kmzbrnoI/mtb-rc/fw/src/railcom/railcom_ll.c

/* RailCom reading implementation */

#include "railcom_ll.h"
#include "assert.h"
#include "stm32f1xx_hal.h"
#include "gpio.h"
#include <string.h>

/* Local variables -----------------------------------------------------------*/

UART_HandleTypeDef huart1;
UART_HandleTypeDef huart2;
TIM_HandleTypeDef htim4; // cutout length counter

volatile RCLLData rclldata[RC_UARTS_COUNT];
volatile uint8_t uart1_input_byte;
volatile uint8_t uart2_input_byte;
volatile bool rc_receiving = false;
volatile RCLLDiag rc_ll_diag;

/* Private prototypes --------------------------------------------------------*/

static void _rc1_init(void);
static void _rc2_init(void);
static void _tim4_init(void);

void _rcll_uart_rx_complete(UART_HandleTypeDef *huart);

static void cutout_start(void);
static void cutout_end(void);
static void cutout_timeout(void);
static uint16_t cutout_length_us(void);

/* Implementation ------------------------------------------------------------*/

/* Init & deinit -------------------------------------------------------------*/

void railcom_ll_init(void) {
    _rc1_init();
    _rc2_init();
    _tim4_init();

    for (size_t i = 0; i < RC_UARTS_COUNT; i++) {
        rclldata[i].ready_to_parse = false;
        rclldata[i].ch1.size = 0;
        rclldata[i].ch2.size = 0;
    }
    rc_receiving = false;

    memset((void*)&rc_ll_diag, 0, sizeof(rc_ll_diag));
}

void _rc1_init(void) {
    __HAL_RCC_USART1_CLK_ENABLE();

    huart1.Instance = USART1;
    huart1.Init.BaudRate = RC_BAUDRATE;
    huart1.Init.WordLength = UART_WORDLENGTH_8B;
    huart1.Init.StopBits = UART_STOPBITS_1;
    huart1.Init.Parity = UART_PARITY_NONE;
    huart1.Init.Mode = UART_MODE_RX;
    huart1.Init.HwFlowCtl = UART_HWCONTROL_NONE;
    huart1.Init.OverSampling = UART_OVERSAMPLING_16;
    assert_param(HAL_UART_Init(&huart1) == HAL_OK);

    gpio_pin_init(pin_rc1, GPIO_MODE_INPUT, GPIO_NOPULL, GPIO_SPEED_FREQ_HIGH, false);

    /* USART1 interrupt Init */
    HAL_NVIC_SetPriority(USART1_IRQn, 0, 0);
    HAL_NVIC_EnableIRQ(USART1_IRQn);

    assert_param(HAL_UART_RegisterCallback(&huart1, HAL_UART_RX_COMPLETE_CB_ID, _rcll_uart_rx_complete) == HAL_OK);

    // Disable receiver till cutout
    CLEAR_BIT(USART1->CR1, USART_CR1_RE);

    // Start first reading
    assert_param(HAL_UART_Receive_IT(&huart1, (uint8_t*)&uart1_input_byte, 1) == HAL_OK);
}

void _rc2_init(void) {
    __HAL_RCC_USART2_CLK_ENABLE();

    huart2.Instance = USART2;
    huart2.Init.BaudRate = RC_BAUDRATE;
    huart2.Init.WordLength = UART_WORDLENGTH_8B;
    huart2.Init.StopBits = UART_STOPBITS_1;
    huart2.Init.Parity = UART_PARITY_NONE;
    huart2.Init.Mode = UART_MODE_RX;
    huart2.Init.HwFlowCtl = UART_HWCONTROL_NONE;
    huart2.Init.OverSampling = UART_OVERSAMPLING_16;
    assert_param(HAL_UART_Init(&huart2) == HAL_OK);

    gpio_pin_init(pin_rc2, GPIO_MODE_INPUT, GPIO_NOPULL, GPIO_SPEED_FREQ_HIGH, false);

    /* USART2 interrupt Init */
    HAL_NVIC_SetPriority(USART2_IRQn, 0, 0);
    HAL_NVIC_EnableIRQ(USART2_IRQn);

    assert_param(HAL_UART_RegisterCallback(&huart2, HAL_UART_RX_COMPLETE_CB_ID, _rcll_uart_rx_complete) == HAL_OK);

    // Disable receiver till cutout
    CLEAR_BIT(USART2->CR1, USART_CR1_RE);

    // Start first reading
    assert_param(HAL_UART_Receive_IT(&huart2, (uint8_t*)&uart2_input_byte, 1) == HAL_OK);
}

void _tim4_init(void) {
    // TIM4 increment each 1 us, interrupt on timeout
    __HAL_RCC_TIM4_CLK_ENABLE();

    htim4.Instance = TIM4;
    htim4.Init.Prescaler = 48; // 48 MHz / 48 -> 1 us
    htim4.Init.CounterMode = TIM_COUNTERMODE_UP;
    htim4.Init.Period = RC_CUTOUT_TIMEOUT;
    htim4.Init.ClockDivision = TIM_CLOCKDIVISION_DIV1;
    htim4.Init.AutoReloadPreload = TIM_AUTORELOAD_PRELOAD_DISABLE;
    assert_param(HAL_TIM_Base_Init(&htim4) == HAL_OK);

    /* TIM4 interrupt Init */
    HAL_NVIC_SetPriority(TIM4_IRQn, 0, 0);
    HAL_NVIC_EnableIRQ(TIM4_IRQn);
}

void railcom_ll_deinit(void) {
    __HAL_RCC_USART1_CLK_DISABLE();
    gpio_pin_deinit(pin_rc1);
    HAL_NVIC_DisableIRQ(USART1_IRQn);

    __HAL_RCC_USART2_CLK_DISABLE();
    gpio_pin_deinit(pin_rc2);
    HAL_NVIC_DisableIRQ(USART2_IRQn);
}

/* Cutout --------------------------------------------------------------------*/

void TIM4_IRQHandler(void) {
    // Cutout timeout
    HAL_TIM_IRQHandler(&htim4);
    cutout_timeout();
}

void gpio_on_cutout_change(void) {
    if (is_cutout())
        cutout_start();
    else
        cutout_end();
}

bool is_cutout(void) {
    return gpio_pin_read(pin_cutout);
}

void cutout_start(void) {
    TIM4->CNT = 0;
    assert_param(HAL_TIM_Base_Start_IT(&htim4) == HAL_OK);
    assert_param(!rc_receiving);

    if ((!rclldata[0].ready_to_parse) && (!rclldata[1].ready_to_parse)) {
        rc_receiving = true;
        for (size_t i = 0; i < RC_UARTS_COUNT; i++) {
            rclldata[i].ch1.size = 0;
            rclldata[i].ch2.size = 0;
        }
    } else {
        rc_ll_diag.cutouts_no_ready_to_parse++;
    }

    rc_ll_diag.cutouts_started++;

    SET_BIT(USART1->CR1, USART_CR1_RE);
    SET_BIT(USART2->CR1, USART_CR1_RE);
}

void cutout_end(void) {
    assert_param(HAL_TIM_Base_Stop(&htim4) == HAL_OK);

    for (size_t i = 0; i < RC_UARTS_COUNT; i++) {
        if ((rc_receiving) && (rclldata[i].ch1.size > 0)) {
            rclldata[i].ready_to_parse = true;
            rc_ll_diag.cutouts_data_ch1++;
        }
        if ((rc_receiving) && (rclldata[i].ch2.size > 0)) {
            rclldata[i].ready_to_parse = true;
            rc_ll_diag.cutouts_data_ch2++;
        }
    }
    rc_receiving = false;
    rc_ll_diag.cutouts_finished++;
    CLEAR_BIT(USART1->CR1, USART_CR1_RE);
    CLEAR_BIT(USART2->CR1, USART_CR1_RE);
}

void cutout_timeout(void) {
    assert_param(HAL_TIM_Base_Stop(&htim4) == HAL_OK);
    rc_receiving = false;
    rc_ll_diag.cutouts_timeout++;
    CLEAR_BIT(USART1->CR1, USART_CR1_RE);
    CLEAR_BIT(USART2->CR1, USART_CR1_RE);
}

uint16_t cutout_length_us(void) {
    return TIM4->CNT;
}

/* UART RX -------------------------------------------------------------------*/

void USART1_IRQHandler(void) {
    HAL_UART_IRQHandler(&huart1);
}

void USART2_IRQHandler(void) {
    HAL_UART_IRQHandler(&huart2);
}

void _rcll_uart_rx_complete(UART_HandleTypeDef *huart) {
    if (huart == &huart1)
        assert_param(HAL_UART_Receive_IT(&huart1, (uint8_t*)&uart1_input_byte, 1) == HAL_OK);
    else
        assert_param(HAL_UART_Receive_IT(&huart2, (uint8_t*)&uart2_input_byte, 1) == HAL_OK);

    if (!rc_receiving)
        return;

    volatile RCLLData* uartdata = (huart == &huart1) ? &rclldata[0] : &rclldata[1];
    const uint8_t received = (huart == &huart1) ? uart1_input_byte : uart2_input_byte;

    if ((cutout_length_us() < RC_CH1_MAX_LEN) && (uartdata->ch1.size < RC_CH1_SIZE)) {
        uartdata->ch1.buf[uartdata->ch1.size] = received;
        uartdata->ch1.size++;
    } else if (uartdata->ch2.size < RC_CH2_SIZE) {
        uartdata->ch2.buf[uartdata->ch2.size] = received;
        uartdata->ch2.size++;
    }
}
