kmzbrnoI/mtb-rc/fw/src/railcom/railcom_data_protection.c

#include "railcom_data_protection.h"

const uint8_t rc_data_decoder[256] = {
    0xFF, // 0 0b00000000
    0xFF, // 1 0b00000001
    0xFF, // 2 0b00000010
    0xFF, // 3 0b00000011
    0xFF, // 4 0b00000100
    0xFF, // 5 0b00000101
    0xFF, // 6 0b00000110
    0xFF, // 7 0b00000111
    0xFF, // 8 0b00001000
    0xFF, // 9 0b00001001
    0xFF, // 10 0b00001010
    0xFF, // 11 0b00001011
    0xFF, // 12 0b00001100
    0xFF, // 13 0b00001101
    0xFF, // 14 0b00001110
    0xFE, // 15 0b00001111
    0xFF, // 16 0b00010000
    0xFF, // 17 0b00010001
    0xFF, // 18 0b00010010
    0xFF, // 19 0b00010011
    0xFF, // 20 0b00010100
    0xFF, // 21 0b00010101
    0xFF, // 22 0b00010110
    0x33, // 23 0b00010111
    0xFF, // 24 0b00011000
    0xFF, // 25 0b00011001
    0xFF, // 26 0b00011010
    0x34, // 27 0b00011011
    0xFF, // 28 0b00011100
    0x35, // 29 0b00011101
    0x36, // 30 0b00011110
    0xFF, // 31 0b00011111
    0xFF, // 32 0b00100000
    0xFF, // 33 0b00100001
    0xFF, // 34 0b00100010
    0xFF, // 35 0b00100011
    0xFF, // 36 0b00100100
    0xFF, // 37 0b00100101
    0xFF, // 38 0b00100110
    0x3A, // 39 0b00100111
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
};
