kmzbrnoI/mtb-rc/fw/src/diag.h

/* Diagnostics */

#pragma once
#include <stdbool.h>
#include <stdint.h>

#include "railcom_addrs.h" // RC_TRACKS_COUNT

typedef union {
    struct {
        bool addr_zero : 1;
        bool bad_mtbbus_polarity : 1;
    } bits;
    uint8_t all;
} error_flags_t;

extern error_flags_t error_flags;

typedef union { // TODO
    struct {
        bool extrf : 1;
        bool borf : 1;
        bool wdrf : 1;
        bool jtrf : 1;
        bool missed_timer : 1;
        bool vcc_oscilating : 1;
    } bits;
    uint8_t all;
} mtbbus_warn_flags_t;

enum MtbRcMWDV {
    dviRCMWCh1InvalidData = 0,
    dviRCMWCh2InvalidData = 1,
    dviRCMWAddr1ReceivedCountResets = 2,
    dviRCMWAddr2ReceivedCountResets = 3,
    dviRCMWApidAdrLowReceived = 4,
    dviRCMWApidAdrHighReceived = 5,
    dviRCMWCh1AddrAdded = 6,
    dviRCMWCh2AddrAdded = 7,
    dviRCMWCount
};

enum MtbRcDV {
    dvVersion = 0,
    dvState = 1,
    dvUptime = 2,
    dvErrors = 10,
    dvWarnings = 11,
    dvVMCU = 12,
    dvTempMCU = 13,

    dvMtbBusReceived = 16,
    dvMtbBusBadCrc = 17,
    dvMtbBusSent = 18,

    dvRCLLCutoutsStarted = 32,
    dvRCLLCutoutsFinished = 33,
    dvRCLLCutoutsTimeout = 34,
    dvRCLLCutoutsDataCh1 = 35,
    dvRCLLCutoutsDataCh2 = 36,
    dvRCLLCutoutsNoReadyToParse = 37,

    dvRCMWFirst = 40,
    dvRCMWLast = dvRCMWFirst+dviRCMWCount-1,

    dvRCMWTrackFirst = 50,
    dvRCMWTrackLast = dvRCMWTrackFirst+(10*RC_TRACKS_COUNT)-1,

    dvRCDCCPacketsReceived = 130,
    dvRCDCCBadXor = 131,
    dvRCDCCLogical0PreambleSoon = 132,
    dvRCDCCMobileDecodersRead = 133,
};

extern mtbbus_warn_flags_t mtbbus_warn_flags;
extern mtbbus_warn_flags_t mtbbus_warn_flags_old;
extern uint32_t uptime_seconds;

void diag_update(void); // called each 100ms
