kmzbrnoI/mtb-rc/fw/src/railcom/railcom_ll.h

/* RailCom USART low-level reading
 * Output: bytes parsed by RailCom
 */

#pragma once

#include <stdbool.h>
#include <stddef.h>
#include <stdint.h>

#define RC_UARTS_COUNT 2
#define RC_BAUDRATE 250000
#define RC_CH1_SIZE 2 // bytes
#define RC_CH2_SIZE 5 // bytes

#define RC_CUTOUT_TIMEOUT 600 // us (uint16_t)
#define RC_CH1_MAX_LEN 185 // us

/* Higher layers poll rlccdata, when ready_to_parse is true, higher layer can
 * read the data. Once reading is finished, higher layer sets ready_to_parse = false,
 * which is an indication for low-level layer that next reading could be performed.
 */

typedef struct {
    struct {
        uint8_t buf[RC_CH1_SIZE];
        size_t size;
    } ch1;
    struct {
        uint8_t buf[RC_CH2_SIZE];
        size_t size;
    } ch2;
    bool ready_to_parse;
} RCLLData;

extern volatile RCLLData rclldata[RC_UARTS_COUNT];
extern volatile bool rc_receiving;

typedef struct {
    uint32_t cutouts_started;
    uint32_t cutouts_finished;
    uint32_t cutouts_timeout;
    uint32_t cutouts_data_ch1;
    uint32_t cutouts_data_ch2;
    uint32_t cutouts_no_ready_to_parse;
} RCLLDiag;

extern volatile RCLLDiag rc_ll_diag;

void railcom_ll_init(void);
void railcom_ll_deinit(void);

bool is_cutout(void);
