kmzbrnoI/mtb-rc/fw/bootloader/src/mtbbus/mtbbus.h

/* MTBbus communication library (via UART).
 *
 * Before changing uart_output_buf & calling mtbbus_send*, you must check that
 * mtbbus_can_fill_output_buf() is true.
 */

#pragma once

#include <stdio.h>
#include <stdbool.h>

#define MTBBUS_OUTPUT_BUF_MAX_SIZE_USER 120
#define MTBBUS_OUTPUT_BUF_MAX_SIZE 128
#define MTBBUS_INPUT_BUF_MAX_SIZE 128

typedef enum {
    MTBBUS_SPEED_38400 = 1,
    MTBBUS_SPEED_57600 = 2,
    MTBBUS_SPEED_115200 = 3,
    MTBBUS_SPEED_230400 = 4,
    MTBBUS_SPEED_MAX
} MtbBusSpeed;

extern uint8_t mtbbus_output_buf[MTBBUS_OUTPUT_BUF_MAX_SIZE];
extern uint8_t mtbbus_output_buf_size;

extern uint8_t mtbbus_addr;
extern MtbBusSpeed mtbbus_speed;

// ‹data› starts with Command code byte
// ‹size› is amount of data bytes + 1
extern void (*mtbbus_on_receive)(bool broadcast, uint8_t command_code, uint8_t *data, uint8_t data_len);
extern void (*mtbbus_on_sent)();

void mtbbus_init(uint8_t addr, MtbBusSpeed speed);
void mtbbus_deinit(void);
void mtbbus_set_speed(MtbBusSpeed speed);
void mtbbus_update(void);

bool mtbbus_can_fill_output_buf(void);
int mtbbus_send(uint8_t *data, uint8_t size);
int mtbbus_send_buf_autolen(void);
int mtbbus_send_buf(void);

#define MTBBUS_CMD_MOSI_MODULE_INQUIRY 0x01
#define MTBBUS_CMD_MOSI_INFO_REQ 0x02
#define MTBBUS_CMD_MOSI_SET_CONFIG 0x03
#define MTBBUS_CMD_MOSI_GET_CONFIG 0x04
#define MTBBUS_CMD_MOSI_BEACON 0x05
#define MTBBUS_CMD_MOSI_GET_INPUT 0x10
#define MTBBUS_CMD_MOSI_SET_OUTPUT 0x11
#define MTBBUS_CMD_MOSI_RESET_OUTPUTS 0x12
#define MTBBUS_CMD_MOSI_CHANGE_ADDR 0x20
#define MTBBUS_CMD_MOSI_DIAG_VALUE_REQ 0xD0
#define MTBBUS_CMD_MOSI_CHANGE_SPEED 0xE0
#define MTBBUS_CMD_MOSI_FWUPGD_REQUEST 0xF0
#define MTBBUS_CMD_MOSI_WRITE_FLASH 0xF1
#define MTBBUS_CMD_MOSI_WRITE_FLASH_STATUS_REQ 0xF2
#define MTBBUS_CMD_MOSI_SPECIFIC 0xFE
#define MTBBUS_CMD_MOSI_REBOOT 0xFF

#define MTBBUS_CMD_MISO_ACK 0x01
#define MTBBUS_CMD_MISO_ERROR 0x02
#define MTBBUS_CMD_MISO_MODULE_INFO 0x03
#define MTBBUS_CMD_MISO_MODULE_CONFIG 0x04
#define MTBBUS_CMD_MISO_INPUT_CHANGED 0x10
#define MTBBUS_CMD_MISO_INPUT_STATE 0x11
#define MTBBUS_CMD_MISO_OUTPUT_SET 0x12
#define MTBBUS_CMD_MISO_DIAG_VALUE 0xD0
#define MTBBUS_CMD_MISO_WRITE_FLASH_STATUS 0xF2
#define MTBBUS_CMD_MISO_SPECIFIC 0xFE

#define MTBBUS_ERROR_UNKNOWN_COMMAND 0x01
#define MTBBUS_ERROR_UNSUPPORTED_COMMAND 0x02
#define MTBBUS_ERROR_BAD_ADDRESS 0x03
#define MTBBUS_ERROR_BUSY 0x04
